Digitelektro/BackfireHelix/pictures/20240410_193813.jpg

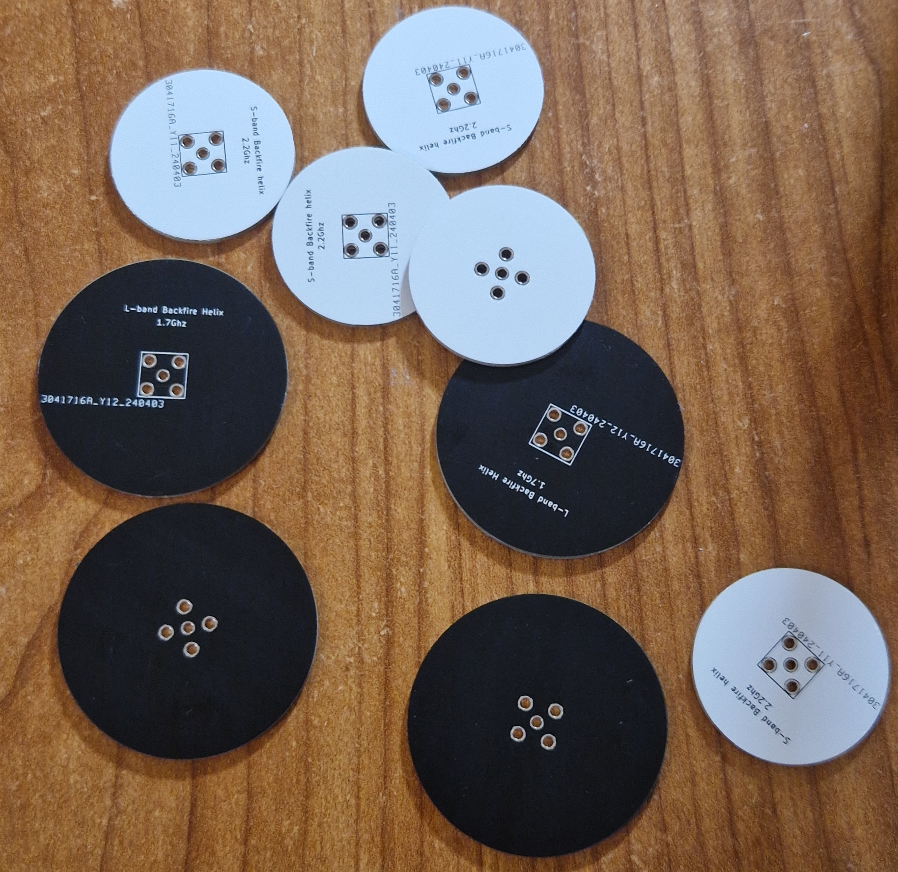
pictures/20240410_193813.jpg
