Digitelektro/BackfireHelix/pictures/DSC_0012.png

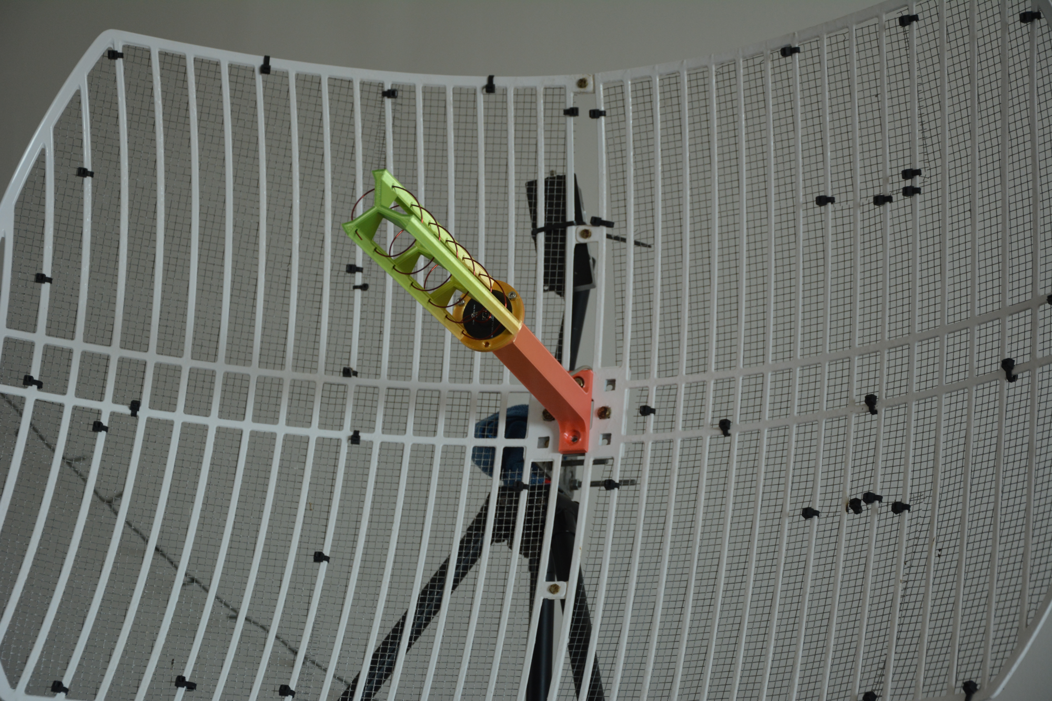
pictures/DSC_0012.png
